fablab-ka/co2-ampel/Software/co2ampel/mqtt.h

/*
  CO2 Ampel - PCB v2.0 + v1.0
  By: FabLab Karlsruhe e.V., Nils Roßmann
  https://github.com/fablab-ka/co2-ampel/
  Date: 13.10.2020
  License: MIT
*/

#ifndef MQTT_H
#define MQTT_H

#include <ESP8266WiFi.h>
#include <PubSubClient.h> // https://github.com/knolleary/pubsubclient (2.8.0)
#include <WiFiClientSecure.h>
#include <ArduinoJson.h> //https://github.com/bblanchon/ArduinoJson (6.16.1, don't install 6.17.0)

#include "ConfigManager.h"
#include "config.h"
#include "led.h"
#include "co2ampel.h"

void loopMQTT(ConfigManager &configManager);
void setupMQTT(ConfigManager &configManager);
void publishValues(ConfigManager &configManager, uint16_t co2, double hum ,double temp, double pressure, double temp2, Color color, float RssI, uint32_t runtime);
void mqttCallback(char* topic, byte* payload, unsigned int length);
void updateFirmware(const char* url);

#endif
